Crane1195/DIYB0XX/LayoutFiles/PDF/MySmallCardboardFrame1/README.md

# DIY Frame1



I made a cheap DIY Frame1 in a cardboard box that is slightly smaller than the real layout, so I tweaked my GCCMX layout a bit to fit the size of this box.
