Crane1195/DIYB0XX/LayoutFiles/DXF/Hammond16x8Case/Hammond_26mm_Support.dxf

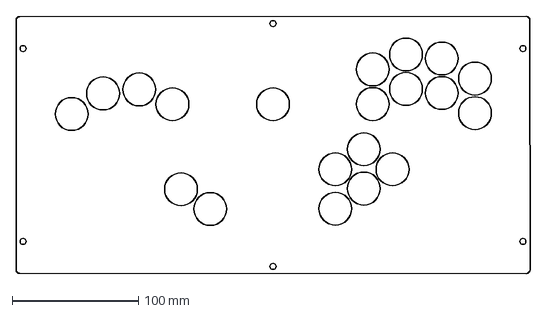
[picture p16: CAD file, 2021-02-19]
LayoutFiles/DXF/Hammond16x8Case/Hammond_26mm_Support.dxf
406.4 x 203.2 mm
