Crane1195/DIYB0XX/LayoutFiles/DXF/Hammond16x8Case/Hammond_24mm_TopPanel.dxf

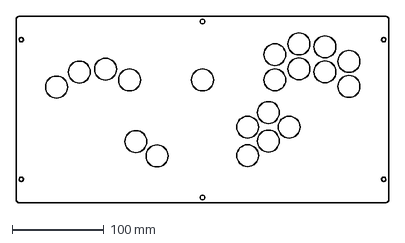
[picture p17: CAD file, 2021-02-19]
LayoutFiles/DXF/Hammond16x8Case/Hammond_24mm_TopPanel.dxf
406.4 x 203.2 mm
