Crane1195/DIYB0XX/code/DIYGCC_USB_Switch_Beta/Joystick.cpp

// Original https://github.com/MHeironimus/ArduinoJoystickLibrary (1.0 branch)
// The purpose of this modified version is for use with a Nintendo Switch.
// It won't work on Windows unless HID().SendReport is changed back at bottom.

/*
  Joystick.cpp

  Copyright (c) 2015, Matthew Heironimus

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
  You should have received a copy of the GNU Lesser General Public
  License along with this library; if not, write to the Free Software
  Foundation, Inc., 51 Franklin St, Fifth Floor, Boston, MA  02110-1301  USA
*/

#include "Joystick.h"

#if defined(_USING_HID)

#define JOYSTICK_REPORT_ID 0x03
#define JOYSTICK_STATE_SIZE 7

static const uint8_t _hidReportDescriptor[] PROGMEM = {
  
	// Joystick
	0x05, 0x01,			      // USAGE_PAGE (Generic Desktop)
	0x09, 0x05,			      // USAGE (Gamepad) - Very important for Switch
	0xa1, 0x01,			      // COLLECTION (Application)
	0x85, JOYSTICK_REPORT_ID, //   REPORT_ID (3)

	// 16 Buttons
	0x05, 0x09,			      //   USAGE_PAGE (Button)
	0x19, 0x01,			      //   USAGE_MINIMUM (Button 1)
	0x29, 0x10,			      //   USAGE_MAXIMUM (Button 32)
	0x15, 0x00,			      //   LOGICAL_MINIMUM (0)
	0x25, 0x01,			      //   LOGICAL_MAXIMUM (1)
	0x75, 0x01,			      //   REPORT_SIZE (1)
	0x95, 0x10,			      //   REPORT_COUNT (16)
	0x55, 0x00,			      //   UNIT_EXPONENT (0)
	0x65, 0x00,			      //   UNIT (None)
	0x81, 0x02,			      //   INPUT (Data,Var,Abs)

	// One Hat switches (8 Positions)
	0x05, 0x01,			      //   USAGE_PAGE (Generic Desktop)
	0x09, 0x39,			      //   USAGE (Hat switch)
	0x15, 0x00,			      //   LOGICAL_MINIMUM (0)
	0x25, 0x07,			      //   LOGICAL_MAXIMUM (7)
	0x35, 0x00,			      //   PHYSICAL_MINIMUM (0)
	0x46, 0x3B, 0x01,	      //   PHYSICAL_MAXIMUM (315)
	0x65, 0x14,			      //   UNIT (Eng Rot:Angular Pos)
	0x75, 0x04,			      //   REPORT_SIZE (4)
	0x95, 0x01,			      //   REPORT_COUNT (1)
	0x81, 0x02,			      //   INPUT (Data,Var,Abs)

	//Padding
	// UNIT (None)
	0x65, 0x00,
	// REPORT_COUNT (1)
	0x95, 0x01,
	// INPUT (Const,Array,Abs)
	0x81, 0x01,

	// X, Y, and Z Axis
	0x15, 0x00,			      //   LOGICAL_MINIMUM (0)
	0x26, 0xff, 0x00,	      //   LOGICAL_MAXIMUM (255)
	0x75, 0x08,			      //   REPORT_SIZE (8)
	0x09, 0x01,			      //   USAGE (Pointer)
	0xA1, 0x00,			      //   COLLECTION (Physical)
	0x09, 0x30,		          //     USAGE (x)
	0x09, 0x31,		          //     USAGE (y)
	0x09, 0x32,		          //     USAGE (z)
	0x09, 0x35,		          //     USAGE (rz)
	0x95, 0x04,		          //     REPORT_COUNT (4)
	0x81, 0x02,		          //     INPUT (Data,Var,Abs)
	0xc0,				      //   END_COLLECTION
                              
	0xc0				      // END_COLLECTION
};

Joystick_::Joystick_()
{
	// Setup HID report structure
	static HIDSubDescriptor node(_hidReportDescriptor, sizeof(_hidReportDescriptor));
	HID().AppendDescriptor(&node);
	
	// Initalize State
	xAxis = 0;
	yAxis = 0;
	zAxis = 0;
	zAxisRotation = 0;
	buttons = 0;
	hatSwitch = -1;
}

void Joystick_::begin(bool initAutoSendState)
{
	autoSendState = initAutoSendState;
	sendState();
}

void Joystick_::end()
{
}

void Joystick_::setButton(uint8_t button, uint8_t value)
{
	if (value == 0)
	{
		releaseButton(button);
	}
	else
	{
		pressButton(button);
	}
}
void Joystick_::pressButton(uint8_t button)
{
	bitSet(buttons, button);
	if (autoSendState) sendState();
}
void Joystick_::releaseButton(uint8_t button)
{
	bitClear(buttons, button);
	if (autoSendState) sendState();
}

void Joystick_::setXAxis(int8_t value)
{
	xAxis = value;
	if (autoSendState) sendState();
}
void Joystick_::setYAxis(int8_t value)
{
	yAxis = value;
	if (autoSendState) sendState();
}
void Joystick_::setZAxis(int8_t value)
{
	zAxis = value;
	if (autoSendState) sendState();
}

void Joystick_::setZAxisRotation(int16_t value)
{
	zAxisRotation = value;
	if (autoSendState) sendState();
}

void Joystick_::setHatSwitch(int16_t value)
{
	hatSwitch = value;
	if (autoSendState) sendState();
}

void Joystick_::sendState()
{
	uint8_t data[JOYSTICK_STATE_SIZE];
	uint32_t buttonTmp = buttons;

	// Split 16 bit button-state into 2 bytes
	data[0] = buttonTmp & 0xFF;		
	buttonTmp >>= 8;
	data[1] = buttonTmp & 0xFF;
	
	if(hatSwitch < 0)
		hatSwitch = 8;
	
	// Pack hat-switch states into a single byte
	data[2] = (B00001111 & hatSwitch);
  
	data[3] = xAxis + 127;
	data[4] = yAxis + 127;
	data[5] = zAxis + 127;
	data[6] = zAxisRotation + 127;

	// HID().SendReport(Report number, array of values in same order as HID descriptor, length)
  
  // For the Switch I needed to replace the first value (Report Number) with the first value.
  HID().SendReport(data[0], data+1, JOYSTICK_STATE_SIZE);
  
  // For Windows you must change this back to:
  //HID().SendReport(JOYSTICK_REPORT_ID, data, JOYSTICK_STATE_SIZE);
}

Joystick_ Joystick;

#endif
